afcaff/2axis_solar/cad/TerryH/Front Door - Back.png

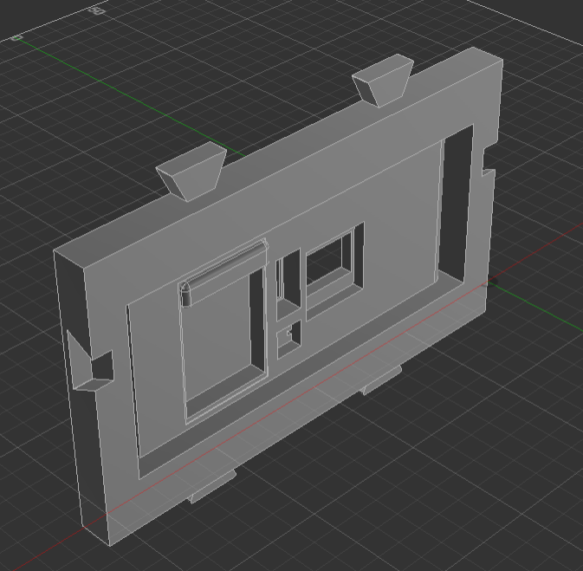
cad/TerryH/Front Door - Back.png
