afcaff/2axis_solar/cad/TerryH/Front Door - Front.png

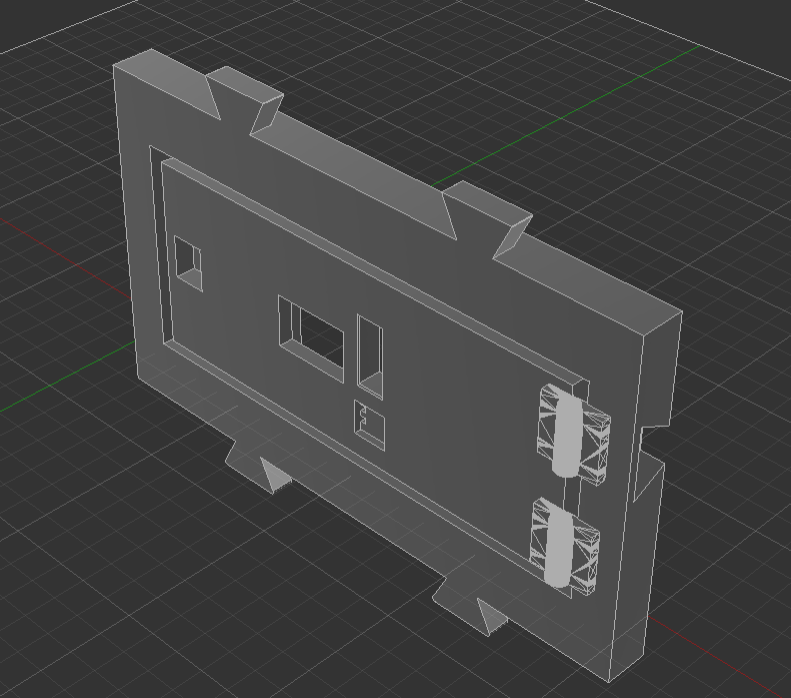
cad/TerryH/Front Door - Front.png
