afcaff/2axis_solar/cad/TerryH/Right Wall.png

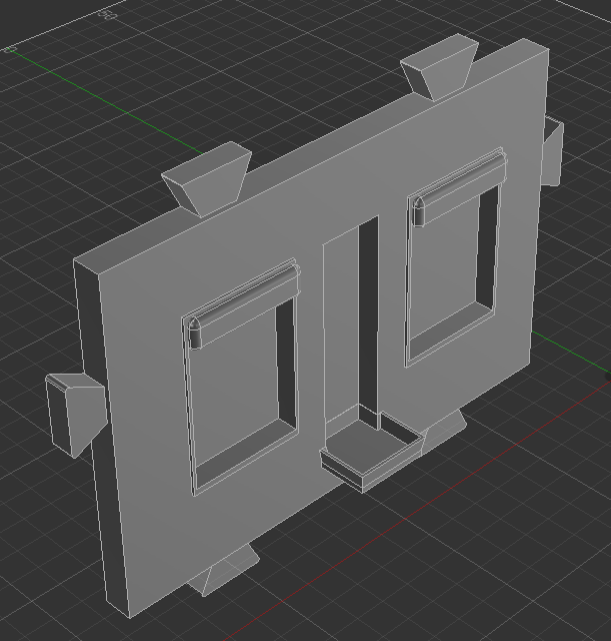
cad/TerryH/Right Wall.png
