afcaff/2axis_solar/cad/TerryH/Top.png

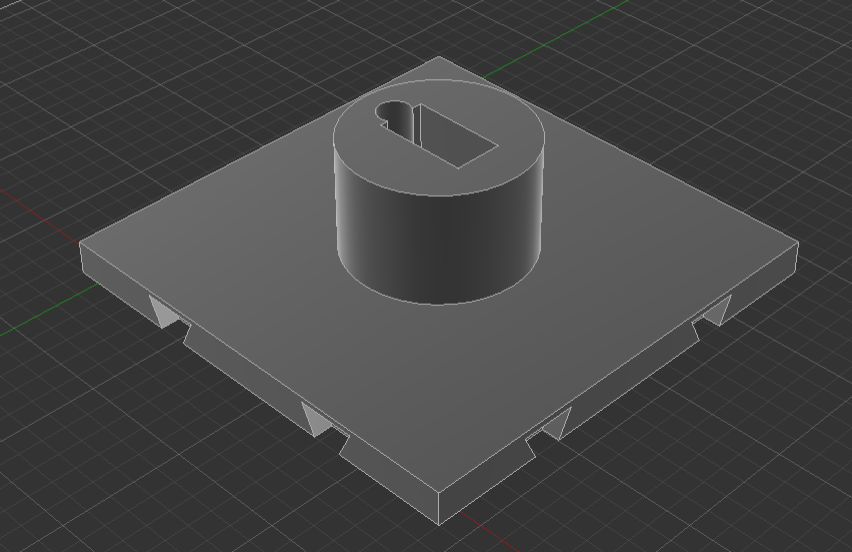
cad/TerryH/Top.png
